abdulkhalamazad/Autonomous-Water-Level-Monitoring-System/Final Product Images/image1.jpg

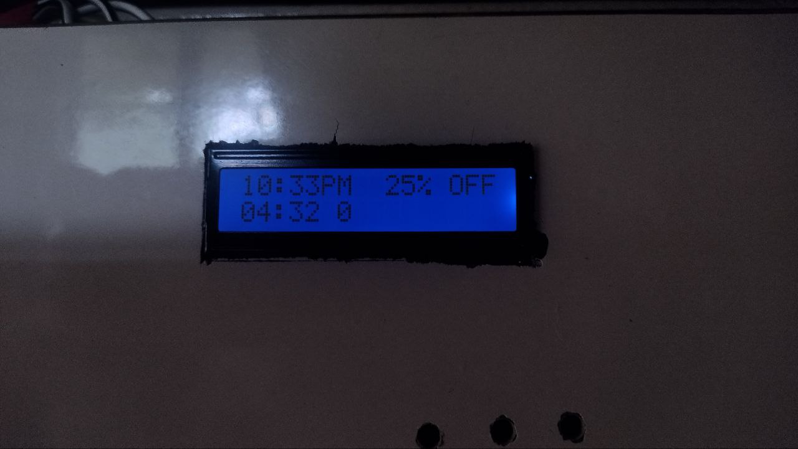
Final Product Images/image1.jpg
