abdulkhalamazad/Autonomous-Water-Level-Monitoring-System/Final Product Images/image4.jpg

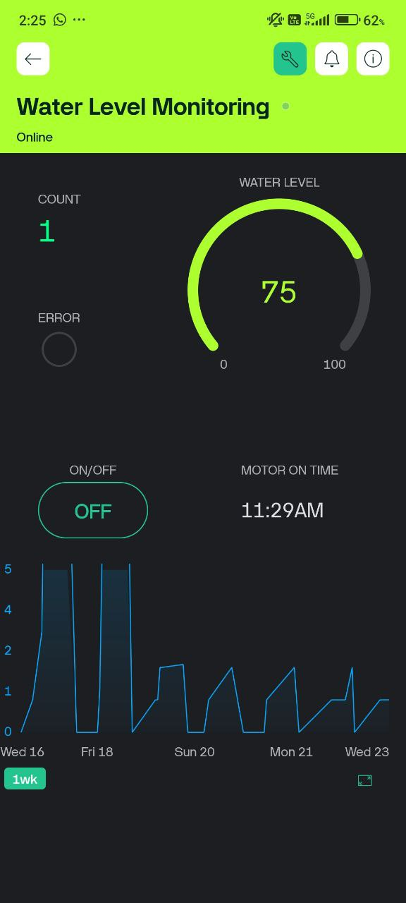
Final Product Images/image4.jpg
