abdulkhalamazad/Autonomous-Water-Level-Monitoring-System/Schematic/Automatic water level monitor.kicad_sch

## KiCad design Schematic/Automatic water level monitor.kicad_sch (2024-10-23)

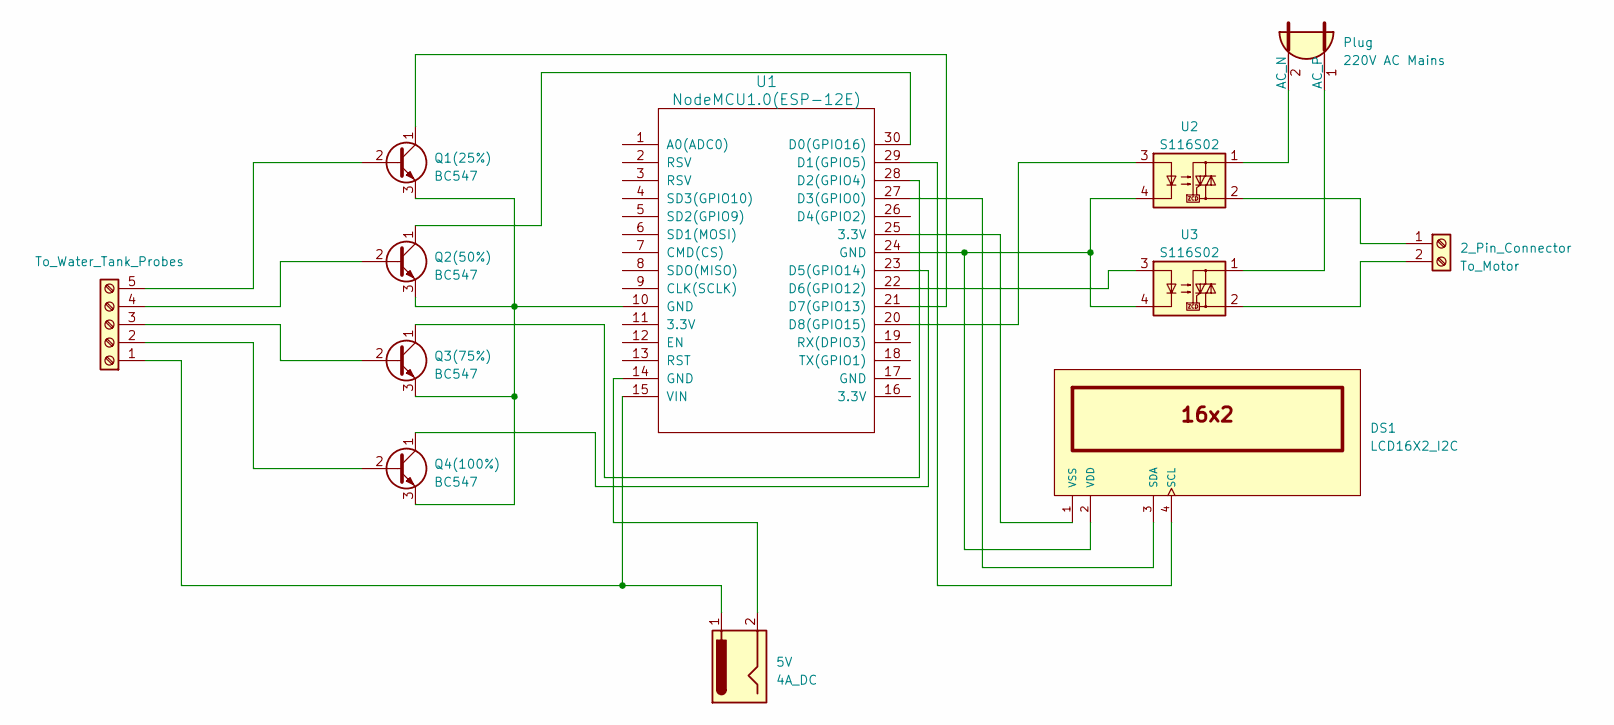
[picture p6: schematic Automatic water level monitor.kicad_sch]

Parts:
2_Pin_Connector: To_Motor
5V: 4A_DC
DS1: LCD16X2_I2C; WC1602A
Plug: 220V AC Mains
Q1(25%), Q2(50%), Q3(75%), Q4(100%): BC547; TO-92_Inline
To_Water_Tank_Probes: (no value)
U1: NodeMCU1.0(ESP-12E)
U2, U3: S116S02; SIP4_Sharp-SSR_P7.62mm_Straight

Connections:
unnamed: 2_Pin_Connector.1, U2.2
unnamed: 2_Pin_Connector.2, U3.2
unnamed: 5V.1, To_Water_Tank_Probes.1, U1.15 (VIN)
unnamed: 5V.2, U1.14 (GND)
unnamed: DS1.1 (VSS), U1.25 (3.3V)
unnamed: DS1.2 (VDD), U1.24 (GND), U2.4, U3.4
unnamed: DS1.3 (SDA), U1.27 (D3(GPIO0))
unnamed: DS1.4 (SCL), U1.29 (D1(GPIO5))
unnamed: Plug.1 (AC_P), U3.1
unnamed: Plug.2 (AC_N), U2.1
unnamed: Q1(25%).1 (C), U1.21 (D7(GPIO13))
unnamed: Q1(25%).2 (B), To_Water_Tank_Probes.5
unnamed: Q1(25%).3 (E), Q2(50%).3 (E), Q3(75%).3 (E), Q4(100%).3 (E), U1.10 (GND)
unnamed: Q2(50%).1 (C), U1.30 (D0(GPIO16))
unnamed: Q2(50%).2 (B), To_Water_Tank_Probes.4
unnamed: Q3(75%).1 (C), U1.28 (D2(GPIO4))
unnamed: Q3(75%).2 (B), To_Water_Tank_Probes.3
unnamed: Q4(100%).1 (C), U1.23 (D5(GPIO14))
unnamed: Q4(100%).2 (B), To_Water_Tank_Probes.2
unnamed: U1.20 (D8(GPIO15)), U2.3
unnamed: U1.22 (D6(GPIO12)), U3.3
